GarethDaviesLondon/esp32-am-transmitter/docs/images/renders/assembly.jpg

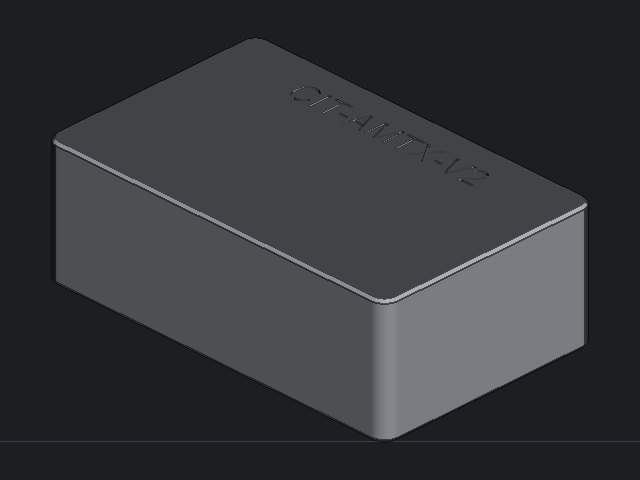
docs/images/renders/assembly.jpg
